chaostreff-flensburg/badge-schwammintelligenz/firmware/led_map.h

// Generiert von tools/gen_led_map.py aus pcb/pcb.kicad_pcb. Nicht von Hand ändern.
#pragma once
#include <stdint.h>

constexpr int LED_COUNT = 110;
constexpr int PIN_COUNT = 11;
constexpr float BOARD_ASPECT = 1.1487f; // Breite / Höhe

struct Led {
  uint8_t col; // Pin-Index der Anode (HIGH zum Leuchten)
  uint8_t row; // Pin-Index der Kathode (LOW zum Leuchten)
  uint8_t x;   // Position 0..255 über die Platinenbreite
  uint8_t y;   // Position 0..255 über die Platinenhöhe (0 = oben)
  uint8_t area; // Hirnareal, Index in AREAS
};

constexpr Led LEDS[LED_COUNT] = {
  { 0,  1, 137, 111, 3}, // D1
  { 0,  2, 138,  80, 3}, // D2
  { 0,  3, 120, 101, 3}, // D3
  { 0,  4,   5, 106, 0}, // D4
  { 0,  5,  16,  91, 0}, // D5
  { 0,  6, 144,  16, 3}, // D6
  { 0,  7, 168,  17, 3}, // D7
  { 0,  8, 238, 165, 5}, // D8
  { 0,  9, 221, 177, 5}, // D9
  { 0, 10, 171, 248, 4}, // D10
  { 1,  0, 105, 125, 1}, // D11
  { 1,  2, 160,  84, 3}, // D12
  { 1,  3, 112,  85, 3}, // D13
  { 1,  4,  21, 113, 0}, // D14
  { 1,  5,  33,  79, 0}, // D15
  { 1,  6, 131,  24, 3}, // D16
  { 1,  7, 188,  25, 3}, // D17
  { 1,  8, 249, 147, 5}, // D18
  { 1,  9, 222, 193, 5}, // D19
  { 1, 10, 163, 239, 4}, // D20
  { 2,  0,  81, 139, 1}, // D21
  { 2,  1, 159, 102, 3}, // D22
  { 2,  3,  98, 104, 0}, // D23
  { 2,  4,  10, 130, 0}, // D24
  { 2,  5,  21,  67, 0}, // D25
  { 2,  6, 117,  17, 3}, // D26
  { 2,  7, 197,  39, 3}, // D27
  { 2,  8, 244, 125, 5}, // D28
  { 2,  9, 209, 207, 5}, // D29
  { 2, 10, 167, 227, 4}, // D30
  { 3,  0,  69, 162, 1}, // D31
  { 3,  1, 155, 121, 3}, // D32
  { 3,  2, 180,  81, 3}, // D33
  { 3,  4,  21, 142, 0}, // D34
  { 3,  5,  40,  55, 0}, // D35
  { 3,  6,  94,  21, 3}, // D36
  { 3,  7, 216,  45, 3}, // D37
  { 3,  8, 246, 104, 5}, // D38
  { 3,  9, 186, 215, 4}, // D39
  { 3, 10, 157, 225, 4}, // D40
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
};

constexpr int AREA_COUNT = 6;
struct Area { uint8_t x, y; }; // Mittelpunkt, gleiche Normierung wie Led
constexpr Area AREAS[AREA_COUNT] = {
  { 48, 106}, // Frontallappen
  {100, 175}, // Temporallappen
  {134, 189}, // Stammhirn
  {146,  72}, // Parietallappen
  {158, 196}, // Kleinhirn
  {236, 174}, // Okzipitallappen
};
